hackerspace-ntnu/HandhaldenSpelkonsoll/components/lvgl_esp32_drivers/lvgl_tft/disp_driver.h

/**
 * @file disp_driver.h
 */

#ifndef DISP_DRIVER_H
#define DISP_DRIVER_H

#ifdef __cplusplus
extern "C" {
#endif

/*********************
 *      INCLUDES
 *********************/
#ifdef LV_LVGL_H_INCLUDE_SIMPLE
#include "lvgl.h"
#else
#include "lvgl/lvgl.h"
#endif

#if defined CONFIG_LV_TFT_DISPLAY_CONTROLLER_ILI9488
#include "ili9488.h"
#endif

/*********************
 *      DEFINES
 *********************/

/**********************
 *      TYPEDEFS
 **********************/

/**********************
 * GLOBAL PROTOTYPES
 **********************/

/* Initialize display */
void *disp_driver_init(void);

/* Display flush callback */
void disp_driver_flush(lv_disp_drv_t * drv, const lv_area_t * area, lv_color_t * color_map);

/* Display rounder callback, used with monochrome dispays */
void disp_driver_rounder(lv_disp_drv_t * disp_drv, lv_area_t * area);

/* Display set_px callback, used with monochrome dispays */
void disp_driver_set_px(lv_disp_drv_t * disp_drv, uint8_t * buf, lv_coord_t buf_w, lv_coord_t x, lv_coord_t y,
    lv_color_t color, lv_opa_t opa);

/**********************
 *      MACROS
 **********************/

#ifdef __cplusplus
} /* extern "C" */
#endif

#endif /*DISP_DRIVER_H*/
